DaveVdE/spdif_gate/photos/IMG_9227.jpeg

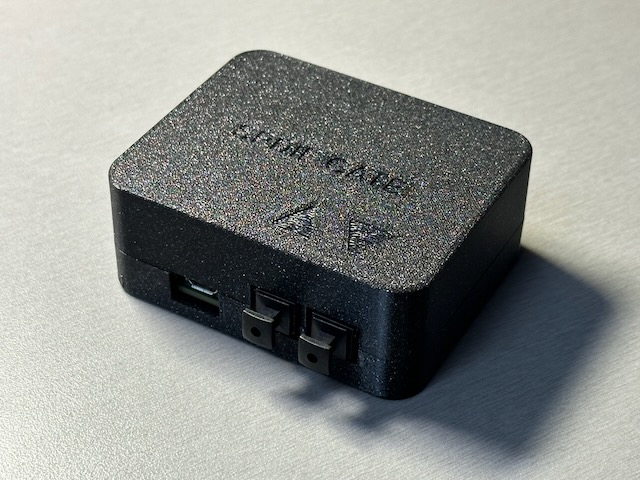
photos/IMG_9227.jpeg
