DaveVdE/spdif_gate/photos/IMG_9228.jpeg

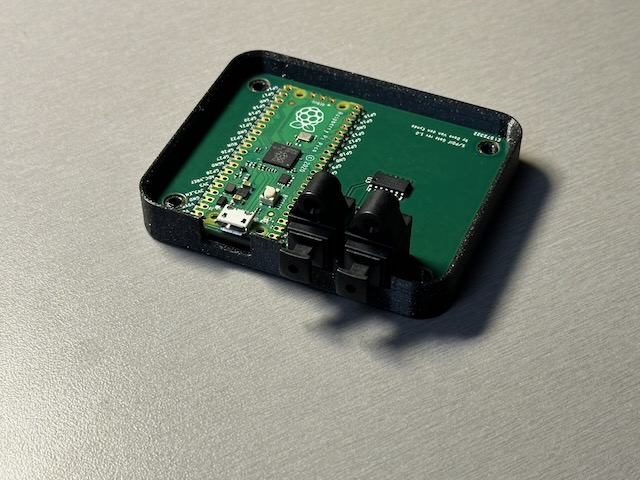
photos/IMG_9228.jpeg
