DaveVdE/spdif_gate/photos/IMG_9229.jpeg

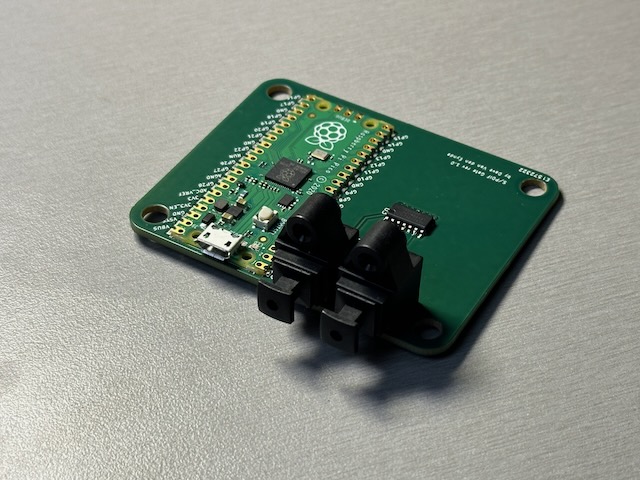
photos/IMG_9229.jpeg
