DaveVdE/spdif_gate/photos/IMG_9230.jpeg

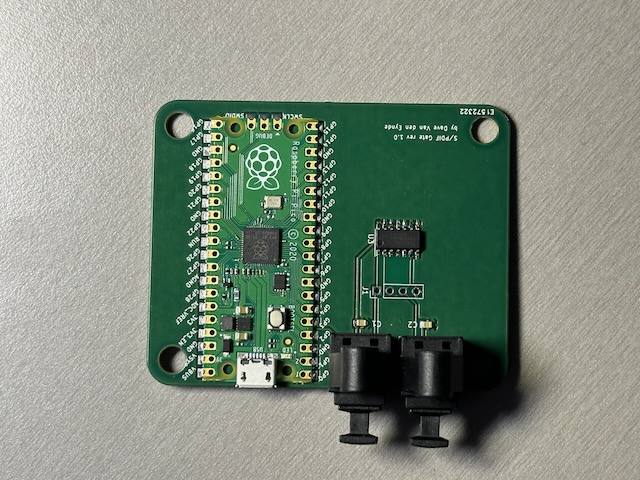
photos/IMG_9230.jpeg
