DaveVdE/spdif_gate/photos/IMG_9231.jpeg

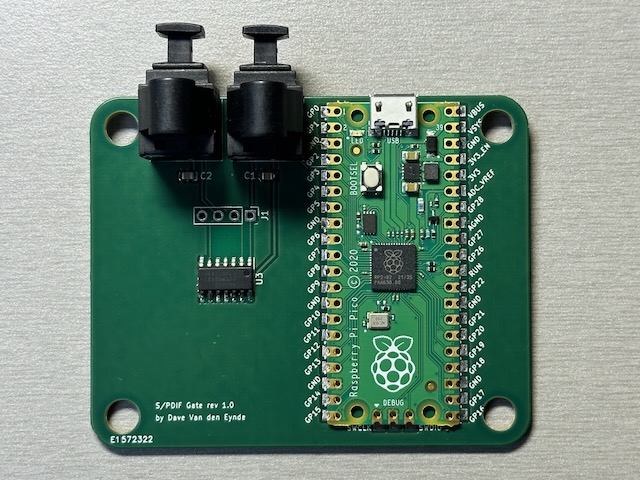
photos/IMG_9231.jpeg
