DaveVdE/spdif_gate/photos/IMG_9232.jpeg

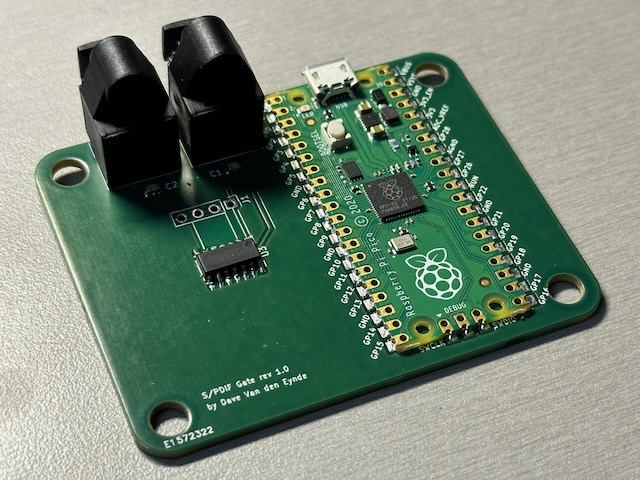
photos/IMG_9232.jpeg
